linzi0928/Weather_Station_V3_OneNet_WiFi_LoRa/WeatherStationV3_DISP/Inc/Asc12X24.h

// ------------------  ASCII字模的数据表 ------------------------ //
// 码表从0x20~0x7e                                                //
// 字库:  实际点阵 16*24，字左对齐共12列，右空4列，合计16列 24行
// 取模：SSD1322控制器 横向取模左高位 
//开发者：www/lcdsoc.com
// -------------------------------------------------------------- //
const unsigned char ASC12X24[] =              // ASCII
{
	0x00,0x00,0x00,0x00,0x00,0x00,0x00,0x00,  // - -
	0x00,0x00,0x00,0x00,0x00,0x00,0x00,0x00,
	0x00,0x00,0x00,0x00,0x00,0x00,0x00,0x00,
	0x00,0x00,0x00,0x00,0x00,0x00,0x00,0x00,
	0x00,0x00,0x00,0x00,0x00,0x00,0x00,0x00,
	0x00,0x00,0x00,0x00,0x00,0x00,0x00,0x00,

	0x00,0x00,0x02,0x00,0x07,0x00,0x07,0x00,  // -!-
	0x07,0x00,0x07,0x00,0x07,0x00,0x07,0x00,
	0x07,0x00,0x07,0x00,0x02,0x00,0x02,0x00,
	0x02,0x00,0x02,0x00,0x02,0x00,0x02,0x00,
	0x02,0x00,0x00,0x00,0x00,0x00,0x02,0x00,
	0x07,0x00,0x07,0x00,0x02,0x00,0x00,0x00,

	0x00,0x00,0x00,0x00,0x39,0xC0,0x39,0xC0,  // -"-
	0x39,0xC0,0x10,0x80,0x10,0x80,0x10,0x80,
	0x00,0x00,0x00,0x00,0x00,0x00,0x00,0x00,
	0x00,0x00,0x00,0x00,0x00,0x00,0x00,0x00,
	0x00,0x00,0x00,0x00,0x00,0x00,0x00,0x00,
	0x00,0x00,0x00,0x00,0x00,0x00,0x00,0x00,

	0x00,0x00,0x00,0x00,0x00,0x00,0x00,0x00,  // -#-
	0x01,0x80,0x31,0x80,0x31,0x80,0x31,0xE0,
	0x3F,0x80,0xF1,0x80,0x31,0x80,0x31,0x80,
	0x31,0x80,0x31,0xE0,0x3F,0x80,0xF1,0x80,
	0x31,0x80,0x31,0x80,0x31,0x80,0x31,0x80,
	0x30,0x00,0x00,0x00,0x00,0x00,0x00,0x00,

	0x00,0x00,0x00,0x00,0x06,0x00,0x06,0x00,  // -$-
	0x3F,0xC0,0x66,0x60,0xC6,0x30,0xC6,0x30,
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

	0x00,0x00,0x00,0x00,0x00,0x00,0x00,0x00,  // -- www/lcdsoc.com
	0x04,0x00,0x04,0x00,0x0E,0x00,0x0A,0x00,
	0x1B,0x00,0x11,0x00,0x31,0x80,0x20,0x80,
	0x60,0xC0,0x40,0x40,0xC0,0x60,0xFF,0xE0,
	0x00,0x00,0x00,0x00,0x00,0x00,0x00,0x00,
	0x00,0x00,0x00,0x00,0x00,0x00,0x00,0x00,
};
