linzi0928/Weather_Station_V3_OneNet_WiFi_LoRa/WeatherStationV3_DISP/Inc/Asc20X40.h

// ------------------  ASCII字模的数据表 ------------------------ //
// 码表从0x20~0x7e                                                //
// 字库:  实际点阵 20*40，字左对齐共20列，右空4列，合计24列 40行
// 取模：SSD1322控制器 横向取模左高位 
// 开发者：www/lcdsoc.com
// -------------------------------------------------------------- //
unsigned char   ASC20X40[] =              // ASCII
{
	0x00,0x00,0x00,0x00,0x00,0x00,0x00,0x00,  // - -
	0x00,0x00,0x00,0x00,0x00,0x00,0x00,0x00,
	0x00,0x00,0x00,0x00,0x00,0x00,0x00,0x00,
	0x00,0x00,0x00,0x00,0x00,0x00,0x00,0x00,
	0x00,0x00,0x00,0x00,0x00,0x00,0x00,0x00,
	0x00,0x00,0x00,0x00,0x00,0x00,0x00,0x00,
	0x00,0x00,0x00,0x00,0x00,0x00,0x00,0x00,
	0x00,0x00,0x00,0x00,0x00,0x00,0x00,0x00,
	0x00,0x00,0x00,0x00,0x00,0x00,0x00,0x00,
	0x00,0x00,0x00,0x00,0x00,0x00,0x00,0x00,
	0x00,0x00,0x00,0x00,0x00,0x00,0x00,0x00,
	0x00,0x00,0x00,0x00,0x00,0x00,0x00,0x00,
	0x00,0x00,0x00,0x00,0x00,0x00,0x00,0x00,
	0x00,0x00,0x00,0x00,0x00,0x00,0x00,0x00,
	0x00,0x00,0x00,0x00,0x00,0x00,0x00,0x00,

	0x00,0x00,0x00,0x00,0x00,0x00,0x00,0x00,  // -!-  www/lcdsoc.com
	0x00,0x00,0x00,0x00,0x00,0x00,0x00,0x00,
	0x00,0x00,0x00,0xE0,0x00,0x00,0xE0,0x00,
	0x00,0xE0,0x00,0x00,0xE0,0x00,0x00,0xE0,
	0x00,0x00,0xE0,0x00,0x00,0xE0,0x00,0x00,
	0xE0,0x00,0x00,0x40,0x00,0x00,0x40,0x00,
	0x00,0x40,0x00,0x00,0x40,0x00,0x00,0x40,
	0x00,0x00,0x40,0x00,0x00,0x40,0x00,0x00,
	0x40,0x00,0x00,0x40,0x00,0x00,0x40,0x00,
	0x00,0x00,0x00,0x00,0x00,0x00,0x00,0x00,
	0x00,0x00,0x00,0x00,0x00,0x00,0x00,0x00,
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
	0x00,0x00,0x00,0x00,0x00,0x00,0x00,0x00,
	0x00,0x00,0x00,0x00,0x00,0x00,0x00,0x00,
	0x00,0x00,0x00,0x00,0x00,0x00,0x00,0x00,
	0x00,0x00,0x00,0x00,0x00,0x00,0x00,0x00,
	0x00,0x00,0x00,0x00,0x00,0x00,0x00,0x00,
	0x00,0x00,0x00,0x00,0x00,0x00,0x00,0x00,
	0x00,0x00,0x00,0x00,0x00,0x00,0x00,0x00,
};
