linzi0928/Weather_Station_V3_OneNet_WiFi_LoRa/WeatherStationV3_DISP/Inc/Asc8X16.h

// ------------------  ASCII字模的数据表 ------------------------ //
// 码表从0x20~0x7e                                                //
// 字库:  实际点阵 8*16，字左对 8列 24行
// 取模：SSD1322控制器 横向取模左高位 
//开发者：www/lcdsoc.com
// -------------------------------------------------------------- //
unsigned char  ASC8X16[] =               
{
	0x00,0x00,0x00,0x00,0x00,0x00,0x00,0x00,  // - -
	0x00,0x00,0x00,0x00,0x00,0x00,0x00,0x00,

	0x00,0x00,0x18,0x3C,0x3C,0x3C,0x18,0x18,  // -!-
	0x18,0x00,0x18,0x18,0x00,0x00,0x00,0x00,

	0x00,0x66,0x66,0x66,0x24,0x00,0x00,0x00,  // -"-
	0x00,0x00,0x00,0x00,0x00,0x00,0x00,0x00,

	0x00,0x00,0x00,0x6C,0x6C,0xFE,0x6C,0x6C,  // -#-
	0x6C,0xFE,0x6C,0x6C,0x00,0x00,0x00,0x00,

	0x18,0x18,0x7C,0xC6,0xC2,0xC0,0x7C,0x06,  // -$- www/lcdsoc.com
	0x86,0xC6,0x7C,0x18,0x18,0x00,0x00,0x00,

	0x00,0x00,0x00,0x00,0xC2,0xC6,0x0C,0x18,  // -%-
	0x30,0x60,0xC6,0x86,0x00,0x00,0x00,0x00,

	0x00,0x00,0x38,0x6C,0x6C,0x38,0x76,0xDC,  // -&-
	0xCC,0xCC,0xCC,0x76,0x00,0x00,0x00,0x00,

	0x00,0x30,0x30,0x30,0x60,0x00,0x00,0x00,  // -'-
	0x00,0x00,0x00,0x00,0x00,0x00,0x00,0x00,

	0x00,0x00,0x0C,0x18,0x30,0x30,0x30,0x30,  // -(-
	0x30,0x30,0x18,0x0C,0x00,0x00,0x00,0x00,

	0x00,0x00,0x30,0x18,0x0C,0x0C,0x0C,0x0C,  // -)-
	0x0C,0x0C,0x18,0x30,0x00,0x00,0x00,0x00,

	0x00,0x00,0x00,0x00,0x00,0x66,0x3C,0xFF,  // -*-
	0x3C,0x66,0x00,0x00,0x00,0x00,0x00,0x00,

	0x00,0x00,0x00,0x00,0x00,0x18,0x18,0x7E,  // -+-
	0x18,0x18,0x00,0x00,0x00,0x00,0x00,0x00,

	0x00,0x00,0x00,0x00,0x00,0x00,0x00,0x00,  // -,-
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

	0x00,0x00,0x00,0x00,0x00,0xC6,0xC6,0xC6,  // -y-
	0xC6,0xC6,0xC6,0x7E,0x06,0x0C,0xF8,0x00,

	0x00,0x00,0x00,0x00,0x00,0xFE,0xCC,0x18,  // -z-
	0x30,0x60,0xC6,0xFE,0x00,0x00,0x00,0x00,

	0x00,0x00,0x0E,0x18,0x18,0x18,0x70,0x18,  // -{-
	0x18,0x18,0x18,0x0E,0x00,0x00,0x00,0x00,

	0x00,0x00,0x18,0x18,0x18,0x18,0x00,0x18,  // -|-
	0x18,0x18,0x18,0x18,0x00,0x00,0x00,0x00,

	0x00,0x00,0x70,0x18,0x18,0x18,0x0E,0x18,  // -}-  www/lcdsoc.com
	0x18,0x18,0x18,0x70,0x00,0x00,0x00,0x00,

	0x00,0x00,0x76,0xDC,0x00,0x00,0x00,0x00,  // -~-
	0x00,0x00,0x00,0x00,0x00,0x00,0x00,0x00,

	0x00,0x00,0x00,0x00,0x10,0x38,0x6C,0xC6,  // --
	0xC6,0xC6,0xFE,0x00,0x00,0x00,0x00,0x00,
};
