linzi0928/Weather_Station_V3_OneNet_WiFi_LoRa/WeatherStationV3_DISP/Src/oled.c

//////////////////////////////////////////////////////////////////////////////////	 
// M31S1322_01_V1 FOR STM32 201505 WWW.LCDSOC.COM

//********************************************************************************
//接口定义参照oled.h文件
#include "oled.h"
#include "stdlib.h"
//定义ASCII库
#include "Asc5x8.h" 	   //ascii 5*8字库
#include "Asc6x12.h" 	   //ascii 8*16字库
#include "Asc8x16.h" 	   //ascii 8*16字库
#include "Asc12x24.h" 	   //ascii 12*24字库
#include "Asc20x40.h" 	   //ascii 20*40字库
//自定义汉字库
#include "HZ12X12_S.h" 	   //12*12宋体自定义汉字库
#include "HZ16X16_S.h" 	   //16*16宋体自定义汉字库
#include "HZ24X24_S.h" 	   //24*24宋体自定义汉字库
// #include "HZ24X24_H.h" 	   //24*24宋体自定义汉字库
// #include "HZ24X24_K.h" 	   //24*24宋体自定义汉字库


//向SSD1325写入一个字节。
//dat:要写入的数据/命令
//cmd:数据/命令标志 0,表示命令;1,表示数据;
void OLED_WR_Byte(u8 dat,u8 cmd)
{	
	u8 i;			  
	if(cmd)
	  OLED_DC_Set();
	else 
	  OLED_DC_Clr();		  
	OLED_CS_Clr();
	for(i=0;i<8;i++)
	{			  
		OLED_SCLK_Clr();
		if(dat&0x80)
		   OLED_SDIN_Set();
		else 
		   OLED_SDIN_Clr();
		OLED_SCLK_Set();
		dat<<=1;   
	}				 		  
	OLED_CS_Set();
	OLED_DC_Set();   	  
} 
  
   
//-----------------OLED端口定义 4线SPI----------------  					   
/* 采用IO口模拟SPI通讯方式驱动oled模块
CS   ~ PE6
RES ~ PE5
DC   ~ PE4
CLK  ~ PE3
DIN ~ PE2
*/  
//初始化SSD1322				    
void OLED_Init(void)
{ 	
 
  OLED_RST_Set();
	HAL_Delay(10);
	OLED_RST_Clr();
	HAL_Delay(10);
	OLED_RST_Set(); 
		
	OLED_WR_Byte(0xAE,OLED_CMD); //	Display Off
	
	OLED_WR_Byte(0xFD,OLED_CMD); // Set Command Lock
	OLED_WR_Byte(0x12,OLED_DATA); //
	
	OLED_WR_Byte(0xB3,OLED_CMD); // Set Clock as 80 Frames/Sec
	OLED_WR_Byte(0x91,OLED_DATA); //  

   	OLED_WR_Byte(0xCA,OLED_CMD); // Set Multiplex Ratio
	OLED_WR_Byte(0x3F,OLED_DATA); // 1/64 Duty (0x0F~0x5F)
   
	OLED_WR_Byte(0xA2,OLED_CMD); // Shift Mapping RAM Counter (0x00~0x3F)
	OLED_WR_Byte(0x00,OLED_DATA); //	
	
	OLED_WR_Byte(0xA1,OLED_CMD); // Set Mapping RAM Display Start Line (0x00~0x7F)
	OLED_WR_Byte(0x00,OLED_DATA); //	

	
	OLED_WR_Byte(0xA0,OLED_CMD); //Set Column Address 0 Mapped to SEG0 
	OLED_WR_Byte(0x14,OLED_DATA);      	//   Default => 0x40
						                //     Horizontal Address Increment
						//     Column Address 0 Mapped to SEG0
						//     Disable Nibble Remap
						//     Scan from COM0 to COM[N-1]
						//     Disable COM Split Odd Even
	OLED_WR_Byte(0x11,OLED_DATA);      	//    Default => 0x01 (Disable Dual COM Mode)

	
	OLED_WR_Byte(0xB5,OLED_CMD); //  Disable GPIO Pins Input
	OLED_WR_Byte(0x00,OLED_DATA); //	
	
    OLED_WR_Byte(0xAB,OLED_CMD); //   Enable Internal VDD Regulator
	OLED_WR_Byte(0x01,OLED_DATA); //

	OLED_WR_Byte(0xB4,OLED_CMD); //  Display Enhancement  
	OLED_WR_Byte(0xA0,OLED_DATA); // Enable External VSL
	OLED_WR_Byte(0xF8,OLED_DATA); // Enhance Low Gray Scale Display Quality

    OLED_WR_Byte(0xC1,OLED_CMD); //  Set Contrast Current 
	OLED_WR_Byte(0xEF,OLED_DATA); //  Default => 0x7F

    OLED_WR_Byte(0xC7,OLED_CMD); //  Master Contrast Current Control 
	OLED_WR_Byte(0xff,OLED_DATA); //  Default => 0x0f (Maximum)

    OLED_WR_Byte(0xB8,OLED_CMD); //  	// Set Gray Scale Table 
	OLED_WR_Byte(0x0C,OLED_DATA); //
	OLED_WR_Byte(0x18,OLED_DATA); //
	OLED_WR_Byte(0x24,OLED_DATA); //
	OLED_WR_Byte(0x30,OLED_DATA); //
	OLED_WR_Byte(0x3C,OLED_DATA); //
	OLED_WR_Byte(0x48,OLED_DATA); //
	OLED_WR_Byte(0x54,OLED_DATA); //
	OLED_WR_Byte(0x60,OLED_DATA); //
	OLED_WR_Byte(0x6C,OLED_DATA); //
	OLED_WR_Byte(0x78,OLED_DATA); //
	OLED_WR_Byte(0x84,OLED_DATA); //
	OLED_WR_Byte(0x90,OLED_DATA); //
	OLED_WR_Byte(0x9C,OLED_DATA); //
	OLED_WR_Byte(0xA8,OLED_DATA); //
	OLED_WR_Byte(0xB4,OLED_DATA); //
 	OLED_WR_Byte(0x00,OLED_CMD); 	// Enable Gray Scale Table

	
	OLED_WR_Byte(0xB1,OLED_CMD); //   Set Phase 1 as 5 Clocks & Phase 2 as 14 Clocks
	OLED_WR_Byte(0xE2,OLED_DATA); //  Default => 0x74 (7 Display Clocks [Phase 2] / 9 Display Clocks [Phase 1])

    OLED_WR_Byte(0xD1,OLED_CMD); //    Enhance Driving Scheme Capability (0x00/0x20)
	OLED_WR_Byte(0xA2,OLED_DATA); //   Normal
	OLED_WR_Byte(0x20,OLED_DATA); //

   
    OLED_WR_Byte(0xBB,OLED_CMD); //     Set Pre-Charge Voltage Level as 0.60*VCC
	OLED_WR_Byte(0x1F,OLED_DATA); //

    OLED_WR_Byte(0xB6,OLED_CMD); //  // Set Second Pre-Charge Period as 8 Clocks 
	OLED_WR_Byte(0x08,OLED_DATA); //

    OLED_WR_Byte(0xBE,OLED_CMD); //  Set Common Pins Deselect Voltage Level as 0.86*VCC 
	OLED_WR_Byte(0x07,OLED_DATA); //  Default => 0x04 (0.80*VCC)

    OLED_WR_Byte(0xA6,OLED_CMD); //     Normal Display Mode (0x00/0x01/0x02/0x03)
	 								  //   Default => 0xA4
						//     0xA4  => Entire Display Off, All Pixels Turn Off
						//     0xA5  => Entire Display On, All Pixels Turn On at GS Level 15
						//     0xA6  => Normal Display
						//     0xA7  => Inverse Display
	 
	 OLED_WR_Byte(0xA9,OLED_CMD); //   Disable Partial Display
     	 	
	Fill_RAM(0x00);
	OLED_WR_Byte(0xAF,OLED_CMD); //	Display On
 

}  

void Set_Column_Address(unsigned char a, unsigned char b)
{
	OLED_WR_Byte(0x15,OLED_CMD);			// Set Column Address
	OLED_WR_Byte(a,OLED_DATA);			//   Default => 0x00
	OLED_WR_Byte(b,OLED_DATA);			//   Default => 0x77
}


void Set_Row_Address(unsigned char a, unsigned char b)
{
	OLED_WR_Byte(0x75,OLED_CMD);			// Set Row Address
	OLED_WR_Byte(a,OLED_DATA);			//   Default => 0x00
	OLED_WR_Byte(b,OLED_DATA);			//   Default => 0x7F
}

void Set_Write_RAM()
{
 
	OLED_WR_Byte(0x5C,OLED_CMD);			// Enable MCU to Write into RAM
}

void Set_Read_RAM()
{
	OLED_WR_Byte(0x5D,OLED_CMD);			// Enable MCU to Read from RAM
}


 void Set_Remap_Format(unsigned char d)
{
	 OLED_WR_Byte(0xA0,OLED_CMD);  			// Set Re-Map / Dual COM Line Mode
  OLED_WR_Byte(d,OLED_DATA);  				//   Default => 0x40
						//     Horizontal Address Increment
						//     Column Address 0 Mapped to SEG0
						//     Disable Nibble Remap
						//     Scan from COM0 to COM[N-1]
						//     Disable COM Split Odd Even
    OLED_WR_Byte(0x11,OLED_DATA); 	 			//   Default => 0x01 (Disable Dual COM Mode)
} 
  void Set_Partial_Display(unsigned char a, unsigned char b, unsigned char c)
{
  	OLED_WR_Byte((0xA8|a),OLED_CMD);		// Default => 0x8F
					
	if(a == 0x00)
	{
	    OLED_WR_Byte(b,OLED_DATA); 
		OLED_WR_Byte(c,OLED_DATA); 
	 
	}
}

void Set_Display_Offset(unsigned char d)
{
	OLED_WR_Byte(0xA2,OLED_CMD);
 	OLED_WR_Byte(d,OLED_DATA);
 
}

void Set_Start_Line(unsigned char d)
{
	OLED_WR_Byte(0xA1,OLED_CMD);	// Set Vertical Scroll by RAM
 	OLED_WR_Byte(d,OLED_DATA);
 
}

void Set_Master_Current(unsigned char d)
{
   OLED_WR_Byte(0xC7,OLED_CMD);	//  Master Contrast Current Control
 	OLED_WR_Byte(d,OLED_DATA);

}

//-=-=-=-=-=-=-=-=-=-=-=-=-=-=-=-=-=-=-=-=-=-=-=-=-=-=-=-=-=-=-=-=-=-=-=
//  Gray Scale Table Setting (Full Screen)
//-=-=-=-=-=-=-=-=-=-=-=-=-=-=-=-=-=-=-=-=-=-=-=-=-=-=-=-=-=-=-=-=-=-=-=
void Set_Gray_Scale_Table()
{

    OLED_WR_Byte(0xB8,OLED_CMD); //  	// Set Gray Scale Table 
	OLED_WR_Byte(0x0C,OLED_DATA); //
	OLED_WR_Byte(0x18,OLED_DATA); //
	OLED_WR_Byte(0x24,OLED_DATA); //
	OLED_WR_Byte(0x30,OLED_DATA); //
	OLED_WR_Byte(0x3C,OLED_DATA); //
	OLED_WR_Byte(0x48,OLED_DATA); //
	OLED_WR_Byte(0x54,OLED_DATA); //
	OLED_WR_Byte(0x60,OLED_DATA); //
	OLED_WR_Byte(0x6C,OLED_DATA); //
	OLED_WR_Byte(0x78,OLED_DATA); //
	OLED_WR_Byte(0x84,OLED_DATA); //
	OLED_WR_Byte(0x90,OLED_DATA); //
	OLED_WR_Byte(0x9C,OLED_DATA); //
	OLED_WR_Byte(0xA8,OLED_DATA); //
	OLED_WR_Byte(0xB4,OLED_DATA); //
 	OLED_WR_Byte(0x00,OLED_CMD); 	// Enable Gray Scale Table

}
void Set_Linear_Gray_Scale_Table()
{
   	OLED_WR_Byte(0xB9,OLED_CMD); //	Set Default Linear Gray Scale Table
 
}
//-=-=-=-=-=-=-=-=-=-=-=-=-=-=-=-=-=-=-=-=-=-=-=-=-=-=-=-=-=-=-=-=-=-=-=
//  Vertical Scrolling (Full Screen)
//
//    a: Scrolling Direction
//       "0x00" (Upward)		向上滚屏
//       "0x01" (Downward)		向下滚屏
//    b: Set Numbers of Row Scroll per Step	  每帧行数
//    c: Set Time Interval between Each Scroll Step	每帧间延时
//-=-=-=-=-=-=-=-=-=-=-=-=-=-=-=-=-=-=-=-=-=-=-=-=-=-=-=-=-=-=-=-=-=-=-=
void Vertical_Scroll(unsigned char a, unsigned char b, unsigned char c)
{
unsigned char i,j;	

	Set_Partial_Display(0x00,0x00,Max_Row);

	switch(a)
	{
		case 0:
			for(i=0;i<(Max_Row+1);i+=b)
			{
				Set_Display_Offset(i+1);
				for(j=0;j<c;j++)
				{
					Delay_us(200);
				}
			}
			break;
		case 1:
			for(i=0;i<(Max_Row+1);i+=b)
			{
				Set_Display_Offset(Max_Row-i);
				for(j=0;j<c;j++)
				{
					Delay_us(200);
				}
			}
			break;
	}
	Set_Partial_Display(0x01,0x00,0x00);
}
  
//-=-=-=-=-=-=-=-=-=-=-=-=-=-=-=-=-=-=-=-=-=-=-=-=-=-=-=-=-=-=-=-=-=-=-=
//  Show Regular Pattern (Full Screen)
 //清屏函数,清屏后,整个屏幕是黑的
//-=-=-=-=-=-=-=-=-=-=-=-=-=-=-=-=-=-=-=-=-=-=-=-=-=-=-=-=-=-=-=-=-=-=-=
void Fill_RAM(unsigned char Data)
{
unsigned char i,j;

	Set_Column_Address(0x00,0x77);
	Set_Row_Address(0x00,0x7F);
	Set_Write_RAM();

	for(i=0;i<128;i++)
	{
		for(j=0;j<120;j++)
		{
			OLED_WR_Byte(Data,OLED_DATA);
		    OLED_WR_Byte(Data,OLED_DATA); 
		}
	}
}
 


 //=-=-=-=-=-=-=-=-=-=-=-=-=-=-=-=-=-=-=-=-=-=-=-=-=-=-=-=-=-=-=-=-=-=-=-=-=-=-=-=
//  www.lcdsoc.com 201505
//	  Data:取值为 0x11，0x22,0x33,0x44,0x55,0x66,0x77,0x88,0x99,0xaa,0xbb,0xcc,0xdd,0xee,0xff, ff最亮
//    a: Line Width		线宽
//    b: Column Address of Start 开始列
//    c: Column Address of End	 结束列
//    d: Row Address of Start	 开始行
//    e: Row Address of End		 结束行
//=-=-=-=-=-=-=-=-=-=-=-=-=-=-=-=-=-=-=-=-=-=-=-=-=-=-=-=-=-=-=-=-=-=-=-=-=-=-=-=
void Draw_Rectangle(unsigned char Data, unsigned char a, unsigned char b, unsigned char c, unsigned char d, unsigned char e)
{
unsigned char i,j,k,l,b1,c1;
	b1=b/4;
	c1=c/4 ;
	k=a%4;
	if(k == 0)
	{
		l=(a/4)-1;
	}
	else
	{
		l=a/4;
	}

	Set_Column_Address(Shift+b1,Shift+c1);
	Set_Row_Address(d,(d+a-1));
	Set_Write_RAM();
	for(i=0;i<(c1-b1+1);i++)
	{
		for(j=0;j<a;j++)
		{
			OLED_WR_Byte(Data,OLED_DATA);
			OLED_WR_Byte(Data,OLED_DATA); 
		}
	}

	Set_Column_Address(Shift+(c1-l),Shift+c1);
	Set_Row_Address(d+a,e-a);
	Set_Write_RAM();
	for(i=0;i<(e-d+1);i++)
	{
		for(j=0;j<(l+1);j++)
		{
			if(j == 0)
			{
				switch(k)
				{
					case 0:
						OLED_WR_Byte(Data,OLED_DATA);
						OLED_WR_Byte(Data,OLED_DATA);
						break;
					case 1:
						OLED_WR_Byte(0x00,OLED_DATA);
						OLED_WR_Byte((Data&0x0F),OLED_DATA);
						 
						break;
					case 2:
					    OLED_WR_Byte(0x00,OLED_DATA);
						OLED_WR_Byte(Data,OLED_DATA);
					
						break;
					case 3:
						OLED_WR_Byte((Data&0x0F),OLED_DATA);
						OLED_WR_Byte(Data,OLED_DATA);
						 
						break;
				}
			}
			else
			{
						OLED_WR_Byte(Data,OLED_DATA);
		             	OLED_WR_Byte(Data,OLED_DATA); 
			}
		}
	}
   

	Set_Column_Address(Shift+b1,Shift+c1);
	Set_Row_Address((e-a+1),e);
	Set_Write_RAM();
	for(i=0;i<(c1-b1+1);i++)
	{
		for(j=0;j<a;j++)
		{
			OLED_WR_Byte(Data,OLED_DATA);
			OLED_WR_Byte(Data,OLED_DATA); 
		 
		}
	}
 
	Set_Column_Address(Shift+b1,Shift+(b1+l));
	Set_Row_Address(d+a,e-a);
	Set_Write_RAM();
	for(i=0;i<(e-d+1);i++)
	{
		for(j=0;j<(l+1);j++)
		{
			if(j == l)
			{
				switch(k)
				{
					case 0:
							OLED_WR_Byte(Data,OLED_DATA);
		                 	OLED_WR_Byte(Data,OLED_DATA); 
						break;
					case 1:
						
						OLED_WR_Byte((Data&0xF0),OLED_DATA);
						OLED_WR_Byte(0x00,OLED_DATA);
						 
						break;
					case 2:
						OLED_WR_Byte(Data,OLED_DATA);
						 OLED_WR_Byte(0x00,OLED_DATA);
					 
						break;
					case 3:
						
						OLED_WR_Byte(Data,OLED_DATA);
						OLED_WR_Byte((Data&0xF0),OLED_DATA);
				 
						break;
				}
			}
			else
			{
					OLED_WR_Byte(Data,OLED_DATA);
		         	OLED_WR_Byte(Data,OLED_DATA); 
			}
		}
	}
}
//-=-=-=-=-=-=-=-=-=-=-=-=-=-=-=-=-=-=-=-=-=-=-=-=-=-=-=-=-=-=-=-=-=-=-=
//  Show Regular Pattern (Partial or Full Screen)
//
//    a: Column Address of Start
//    b: Column Address of End (Total Columns Devided by 4)
//    c: Row Address of Start
//    d: Row Address of End
//-=-=-=-=-=-=-=-=-=-=-=-=-=-=-=-=-=-=-=-=-=-=-=-=-=-=-=-=-=-=-=-=-=-=-=
void Fill_Block(unsigned char Data, unsigned char a, unsigned char b, unsigned char c, unsigned char d)
{
unsigned char i,j;
	
	Set_Column_Address(Shift+a,Shift+b);
	Set_Row_Address(c,d);
	Set_Write_RAM();

	for(i=0;i<(d-c+1);i++)
	{
		for(j=0;j<(b-a+1);j++)
		{
			OLED_WR_Byte(Data,OLED_DATA);
		    OLED_WR_Byte(Data,OLED_DATA); 
		}
	}
}
//-=-=-=-=-=-=-=-=-=-=-=-=-=-=-=-=-=-=-=-=-=-=-=-=-=-=-=-=-=-=-=-=-=-=-=
//  Show Pattern (Partial or Full Screen)
//
//    a: Column Address of Start
//    b: Column Address of End (Total Columns Devided by 4)
//    c: Row Address of Start
//    d: Row Address of End
// 灰度模式下显示一副图片
//-=-=-=-=-=-=-=-=-=-=-=-=-=-=-=-=-=-=-=-=-=-=-=-=-=-=-=-=-=-=-=-=-=-=-=
void Show_Pattern(unsigned char *Data_Pointer, unsigned char a, unsigned char b, unsigned char c, unsigned char d)
{
			 
unsigned char *Src_Pointer;
unsigned char i,j;
 
  //取模时候像素正序	（不能反序与2.7不同）
    Src_Pointer=Data_Pointer;
	Set_Column_Address(Shift+a,Shift+b);
	Set_Row_Address(c,d);
	Set_Write_RAM();
  	for(i=0;i<(d-c+1);i++)
	{
		for(j=0;j<(b-a+1);j++)
		{
			OLED_WR_Byte(*Src_Pointer,OLED_DATA);
			Src_Pointer++;
			OLED_WR_Byte(*Src_Pointer,OLED_DATA);
			Src_Pointer++;
		}
	}

 }
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
